moro3264/microcalculator_6502/kicad/microcalculator_6502/microcalculator_6502.kicad_sch

## KiCad design kicad/microcalculator_6502/microcalculator_6502.kicad_sch (2026-05-16)

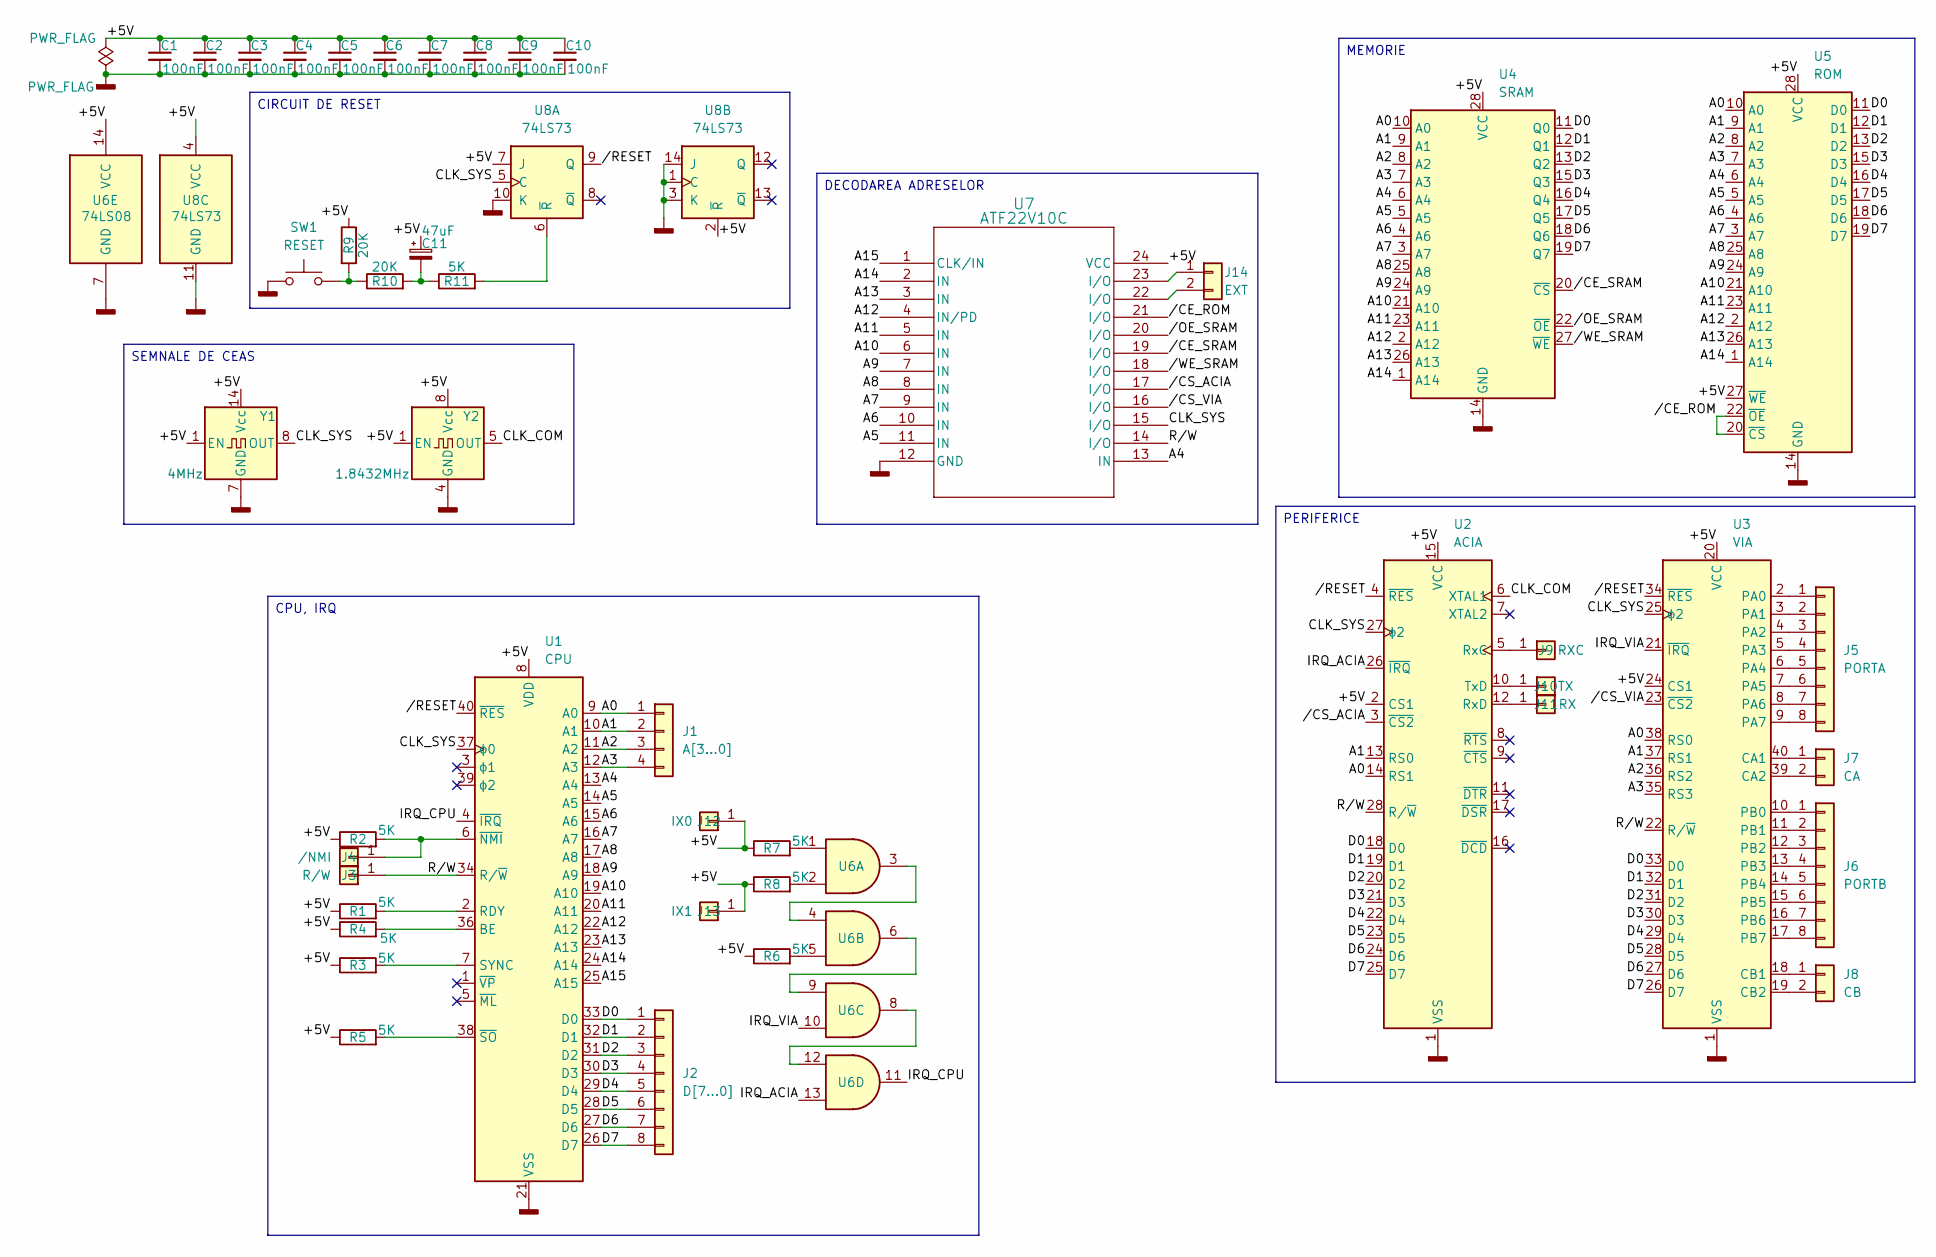
[picture p2: schematic microcalculator_6502.kicad_sch]

Parts:
C1, C2, C3, C4, C5, C6, C7, C8, C9, C10: 100nF; C_Disc_D3.0mm_W2.0mm_P2.50mm
C11: 47uF; CP_Radial_D5.0mm_P2.50mm
J1: A[3...0]; PinHeader_1x04_P2.54mm_Vertical
J2: D[7...0]; PinHeader_1x08_P2.54mm_Vertical
J3: R/W; PinHeader_1x01_P2.54mm_Vertical
J4: /NMI; PinHeader_1x01_P2.54mm_Vertical
J5: PORTA; PinHeader_1x08_P2.54mm_Vertical
J6: PORTB; PinHeader_1x08_P2.54mm_Vertical
J7: CA; PinHeader_1x02_P2.54mm_Vertical
J8: CB; PinHeader_1x02_P2.54mm_Vertical
J9: RXC; PinHeader_1x01_P2.54mm_Vertical
J10: TX; PinHeader_1x01_P2.54mm_Vertical
J11: RX; PinHeader_1x01_P2.54mm_Vertical
J12: IX0; PinHeader_1x01_P2.54mm_Vertical
J13: IX1; PinHeader_1x01_P2.54mm_Vertical
J14: EXT; PinHeader_1x02_P2.54mm_Vertical
R1, R2, R3, R4, R5, R6, R7, R8, R11: 5K; R_Axial_DIN0207_L6.3mm_D2.5mm_P2.54mm_Vertical
R9, R10: 20K; R_Axial_DIN0207_L6.3mm_D2.5mm_P2.54mm_Vertical
SW1: RESET; SW_PUSH_6mm
U1: CPU; DIP-40_W15.24mm
U2: ACIA; DIP-28_W15.24mm
U3: VIA; DIP-40_W15.24mm
U4: SRAM; DIP-28_W15.24mm
U5: ROM; DIP-28_W15.24mm
U6: 74LS08; DIP-14_W7.62mm
U7: ATF22V10C; DIP-24_W7.62mm
U8: 74LS73; DIP-14_W7.62mm
Y1: 4MHz; Oscillator_DIP-14
Y2: 1.8432MHz; Oscillator_DIP-8

Connections:
+5V: C1.1, C2.1, C3.1, C4.1, C5.1, C6.1, C7.1, C8.1, C9.1, C10.1, C11.1, J12.1, J13.1, R1.1, R2.1, R3.1, R4.1, R5.1, R6.1, R7.1, R8.1, R9.1, U1.8 (VDD), U2.2 (CS1), U2.15 (VCC), U3.20 (VCC), U3.24 (CS1), U4.28 (VCC), U5.27 (~WE), U5.28 (VCC), U6.14 (VCC), U7.24 (VCC), U8.2 (~R), U8.4 (VCC), U8.7 (J), Y1.1 (EN), Y1.14 (Vcc), Y2.1 (EN), Y2.8 (Vcc)
A0: J1.1, U1.9 (A0), U2.14 (RS1), U3.38 (RS0), U4.10 (A0), U5.10 (A0)
A1: J1.2, U1.10 (A1), U2.13 (RS0), U3.37 (RS1), U4.9 (A1), U5.9 (A1)
A2: J1.3, U1.11 (A2), U3.36 (RS2), U4.8 (A2), U5.8 (A2)
A3: J1.4, U1.12 (A3), U3.35 (RS3), U4.7 (A3), U5.7 (A3)
A4: U1.13 (A4), U4.6 (A4), U5.6 (A4), U7.13 (IN)
A5: U1.14 (A5), U4.5 (A5), U5.5 (A5), U7.11 (IN)
A6: U1.15 (A6), U4.4 (A6), U5.4 (A6), U7.10 (IN)
A7: U1.16 (A7), U4.3 (A7), U5.3 (A7), U7.9 (IN)
A8: U1.17 (A8), U4.25 (A8), U5.25 (A8), U7.8 (IN)
A9: U1.18 (A9), U4.24 (A9), U5.24 (A9), U7.7 (IN)
A10: U1.19 (A10), U4.21 (A10), U5.21 (A10), U7.6 (IN)
A11: U1.20 (A11), U4.23 (A11), U5.23 (A11), U7.5 (IN)
A12: U1.22 (A12), U4.2 (A12), U5.2 (A12), U7.4 (IN/PD)
A13: U1.23 (A13), U4.26 (A13), U5.26 (A13), U7.3 (IN)
A14: U1.24 (A14), U4.1 (A14), U5.1 (A14), U7.2 (IN)
A15: U1.25 (A15), U7.1 (CLK/IN)
CLK_COM: U2.6 (XTAL1), Y2.5 (OUT)
CLK_SYS: U1.37 (ϕ0), U2.27 (ϕ2), U3.25 (ϕ2), U7.15 (I/O), U8.5 (C), Y1.8 (OUT)
D0: J2.1, U1.33 (D0), U2.18 (D0), U3.33 (D0), U4.11 (Q0), U5.11 (D0)
D1: J2.2, U1.32 (D1), U2.19 (D1), U3.32 (D1), U4.12 (Q1), U5.12 (D1)
D2: J2.3, U1.31 (D2), U2.20 (D2), U3.31 (D2), U4.13 (Q2), U5.13 (D2)
D3: J2.4, U1.30 (D3), U2.21 (D3), U3.30 (D3), U4.15 (Q3), U5.15 (D3)
D4: J2.5, U1.29 (D4), U2.22 (D4), U3.29 (D4), U4.16 (Q4), U5.16 (D4)
D5: J2.6, U1.28 (D5), U2.23 (D5), U3.28 (D5), U4.17 (Q5), U5.17 (D5)
D6: J2.7, U1.27 (D6), U2.24 (D6), U3.27 (D6), U4.18 (Q6), U5.18 (D6)
D7: J2.8, U1.26 (D7), U2.25 (D7), U3.26 (D7), U4.19 (Q7), U5.19 (D7)
GNDD: C1.2, C2.2, C3.2, C4.2, C5.2, C6.2, C7.2, C8.2, C9.2, C10.2, SW1.1, U1.21 (VSS), U2.1 (VSS), U3.1 (VSS), U4.14 (GND), U5.14 (GND), U6.7 (GND), U7.12 (GND), U8.1 (C), U8.3 (K), U8.10 (K), U8.11 (GND), U8.14 (J), Y1.7 (GND), Y2.4 (GND)
IRQ_ACIA: U2.26 (~IRQ), U6.13
IRQ_CPU: U1.4 (~IRQ), U6.11
IRQ_VIA: U3.21 (~IRQ), U6.10
unnamed: C11.2, R10.2, R11.1
unnamed: J4.1, R2.2, U1.6 (~NMI)
unnamed: J5.1, U3.2 (PA0)
unnamed: J5.2, U3.3 (PA1)
unnamed: J5.3, U3.4 (PA2)
unnamed: J5.4, U3.5 (PA3)
unnamed: J5.5, U3.6 (PA4)
unnamed: J5.6, U3.7 (PA5)
unnamed: J5.7, U3.8 (PA6)
unnamed: J5.8, U3.9 (PA7)
unnamed: J6.1, U3.10 (PB0)
unnamed: J6.2, U3.11 (PB1)
unnamed: J6.3, U3.12 (PB2)
unnamed: J6.4, U3.13 (PB3)
unnamed: J6.5, U3.14 (PB4)
unnamed: J6.6, U3.15 (PB5)
unnamed: J6.7, U3.16 (PB6)
unnamed: J6.8, U3.17 (PB7)
unnamed: J7.1, U3.40 (CA1)
unnamed: J7.2, U3.39 (CA2)
unnamed: J8.1, U3.18 (CB1)
unnamed: J8.2, U3.19 (CB2)
unnamed: J9.1, U2.5 (RxC)
unnamed: J10.1, U2.10 (TxD)
unnamed: J11.1, U2.12 (RxD)
unnamed: J14.1, U7.23 (I/O)
unnamed: J14.2, U7.22 (I/O)
unnamed: R1.2, U1.2 (RDY)
unnamed: R3.2, U1.7 (SYNC)
unnamed: R4.2, U1.36 (BE)
unnamed: R5.2, U1.38 (~SO)
unnamed: R6.2, U6.5
unnamed: R7.2, U6.1
unnamed: R8.2, U6.2
unnamed: R9.2, R10.1, SW1.2
unnamed: R11.2, U8.6 (~R)
unnamed: U6.3, U6.4
unnamed: U6.6, U6.9
unnamed: U6.8, U6.12
R/W: J3.1, U1.34 (R/~W), U2.28 (R/~W), U3.22 (R/~W), U7.14 (I/O)
/CE_ROM: U5.20 (~CS), U5.22 (~OE), U7.21 (I/O)
/CE_SRAM: U4.20 (~CS), U7.19 (I/O)
/CS_ACIA: U2.3 (~CS2), U7.17 (I/O)
/CS_VIA: U3.23 (~CS2), U7.16 (I/O)
/OE_SRAM: U4.22 (~OE), U7.20 (I/O)
/RESET: U1.40 (~RES), U2.4 (~RES), U3.34 (~RES), U8.9 (Q)
/WE_SRAM: U4.27 (~WE), U7.18 (I/O)

Notes on the sheet:
DECODAREA ADRESELOR
SEMNALE DE CEAS
PERIFERICE
CIRCUIT DE RESET
MEMORIE
CPU, IRQ
