moro3264/microcalculator_6502/src/LCD.asm

;   Driver pentru afisaje LCD alfanumerice (HD44780)
;   Faciliteaza interfatarea unui LCD prin 6522
;       Subrutine:
;   *   LCD_INIT
;   *   LCD_CMD
;   *   LCD_CHR
;   *   LCD_STR
;   *   LCD_CLEAR

.include "adrese_io.inc"
.include "VIA.inc"

.define _LCD_L1_STR         $0000
.define _LCD_VAL_TMP        $2FFF

.CODE
LCD_INIT:
    PHA

    LDA #$02
    JSR LCD_CMD
    LDA #$28
    JSR LCD_CMD
    LDA #$06
    JSR LCD_CMD
    LDA #$0C
    JSR LCD_CMD
    JSR LCD_CLEAR

    PLA
    RTS

;   VIA_PORTB ~ LCD
;   7   6   5   4   3   2   1   0
;   7   6   5   4   X   RS  E   X
LCD_CMD:
    PHA 

    STA _LCD_VAL_TMP
    AND #$F0
    ORA #$02           ;   E = 1
    STA VIA_PORTB

    JSR DELAY

    AND #$F0
    STA VIA_PORTB           ;E = 0

    JSR DELAY

    LDA _LCD_VAL_TMP
    ROL A           
    ROL A           
    ROL A           
    ROL A           
    AND #$F0
    ORA #$02        
    STA VIA_PORTB       

    JSR DELAY

    AND #$F0
    STA VIA_PORTB

    JSR DELAY
    
    PLA
    RTS

;   VIA_PORTB
;   7   6   5   4   3   2   1   0
;   7   6   5   4   X   RS  E   X

LCD_CHR:
    PHA

    STA _LCD_VAL_TMP    ;
    AND #$F0            ;
    ORA #$06            ;   RS = 1 si E = 1

    STA VIA_PORTB
    JSR DELAY

    AND #$F4            ;   RS = 1 si E = 0

    STA VIA_PORTB
    JSR DELAY

    LDA _LCD_VAL_TMP
    ROL A
    ROL A
    ROL A
    ROL A
    AND #$F0
    ORA #$06        ;   RS = 1 si E = 1

    STA VIA_PORTB
    JSR DELAY

    AND #$F4        ;   RS = 1 si E = 0

    STA VIA_PORTB
    JSR DELAY

    PLA
    RTS

LCD_STR: 
    PHA
    PHY
    
    STA _LCD_L1_STR
    STY _LCD_L1_STR + 1

    LDY #$00
@LCD_STR_AFISARE_CHR:
    LDA (_LCD_L1_STR), Y
    BEQ @LCD_STR_FINAL
    JSR LCD_CHR
    INY
    JMP @LCD_STR_AFISARE_CHR
@LCD_STR_FINAL:
    PLY
    PLA

    RTS
    
;   subrutina de delay
DELAY:
    PHA
    PHX

    LDA #$60
@DELAY_1:
    TAX
@DELAY_0:
    DEX
    BNE @DELAY_0
    DEC
    BNE @DELAY_1

    PLX
    PLA
    RTS

LCD_CLEAR:
    PHA
    LDA #$01
    JSR LCD_CMD
    LDA #$80
    JSR LCD_CMD
    PLA
    RTS

.export LCD_INIT
.export LCD_CMD
.export LCD_CHR
.export LCD_STR
.export LCD_CLEAR
.export DELAY
